arthurbenemann/usmd/usmd.asc

JMK021BJ103KK: cap; {10n*0.8}; x8
R1: res; 10Meg
R2: res; 1k
U1: NE555
V1: battery; 3v
Named nets: 0, vin, rc
.tran 0 5 1
